TannerHollis/Microphone_Amplifier/LTSpiceIV/Amplifier Circuit.asc

C1: cap; 10µ
C2: cap; 15.4n
R1: res; 47k
R2: res; 47k
R3: res; 470
R4: res; 470
R5: res; 4.7k
R6: res; 470
U1: UniversalOpamp2
U2: UniversalOpamp2
V1: voltage; 3.3V
V2: voltage; SINE(0 0.01 22.05k); AC 1 0
Named nets: 0, 1V65
.ac oct 1 1 200k
